carrotIndustries/cyclotron-mini/mech/cyclotron-dev-mount.FCStd

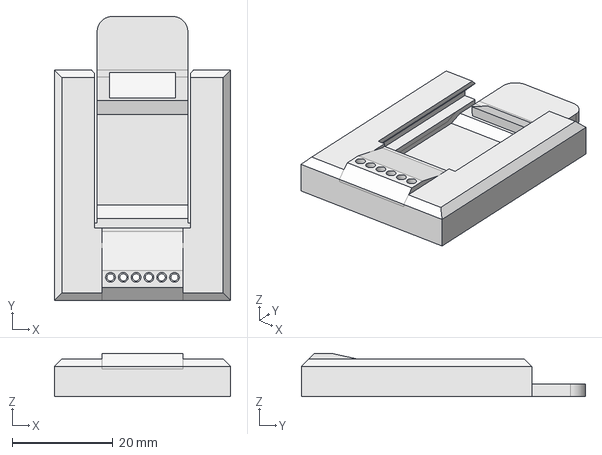
[picture p22: CAD file, 2021-12-24]
mech/cyclotron-dev-mount.FCStd
35.0 x 56.4 x 8.57 mm
