carrotIndustries/cyclotron-mini/hw/pool/3d_models/cache/6d752bc3-29b3-45df-8cf2-1e3aacefbcc6/3d_models/diode/D_SOD-523.step

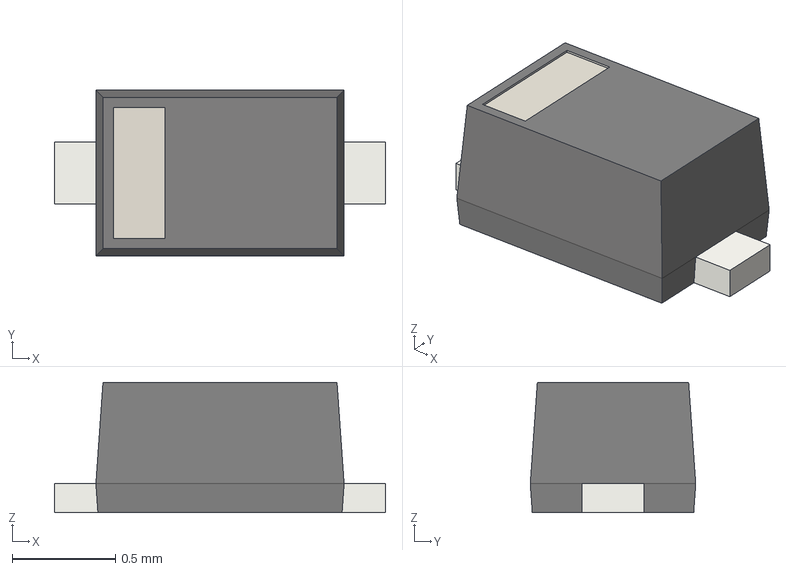
[picture p23: CAD file, 2021-12-24]
hw/pool/3d_models/cache/6d752bc3-29b3-45df-8cf2-1e3aacefbcc6/3d_models/diode/D_SOD-523.step
1.60 x 0.8 x 0.63 mm
