carrotIndustries/cyclotron-mini/hw/pool/3d_models/cache/6d752bc3-29b3-45df-8cf2-1e3aacefbcc6/3d_models/ic/so/SOT-23-5.step

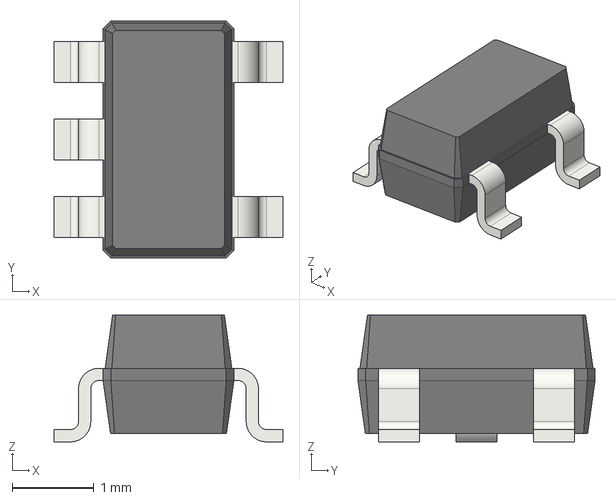
[picture p24: CAD file, 2021-12-24]
hw/pool/3d_models/cache/6d752bc3-29b3-45df-8cf2-1e3aacefbcc6/3d_models/ic/so/SOT-23-5.step
2.80 x 2.90 x 1.55 mm
