carrotIndustries/cyclotron-mini/mech/cyclotron-case.FCStd

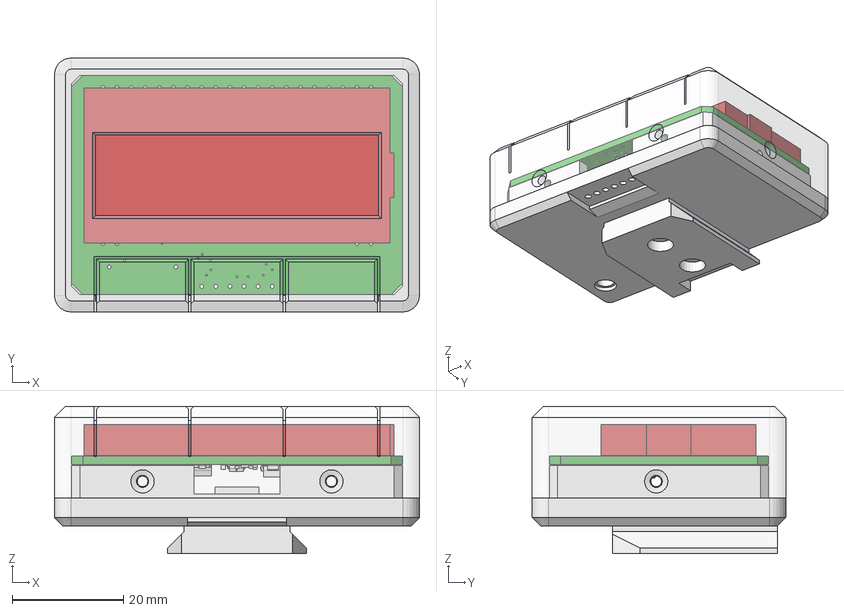
[picture p26: CAD file, 2021-12-24]
mech/cyclotron-case.FCStd
65.7 x 45.7 x 26.5 mm
top
bottom
dovetail
main-PCB
main-C1-1
main-C2-1
main-C3-1
main-C4-1
main-C5-1
main-C6-1
main-C7-1
main-C10-1
main-C11-1
main-C12-1
main-C16-1
main-C19-1
main-C20-1
main-C21-1
main-C22-1
main-D1-1
main-D2-1
main-D3-1
main-D4-1
main-D5-1
main-D8-1
main-D9-1
main-D10-1
main-D11-1
main-D12-1
main-D13-1
main-D14-1
main-D15-1
main-D16-1
main-D17-1
main-DS1-1
main-Q1-1
main-Q2-1
main-Q3-1
main-R1-1
main-R2-1
main-R3-1
main-R4-1
main-R5-1
main-R6-1
main-R7-1
main-R8-1
main-R9-1
main-R10-1
main-R19-1
main-R20-1
main-R21-1
main-R22-1
main-R23-1
main-R24-1
main-U2-1
main-U6-1
main-U7-1
main-Y1-1
