carrotIndustries/cyclotron-mini/fw/app/apps.h

#pragma once
#include "app.h"

extern const app_t app_app_launcher;
extern const app_t app_app_config;
extern const app_t app_app_debug;
extern const app_t app_app_dash;
extern const app_t app_app_blinken;
